GenericLab/TurbiGnUSB/TurbidiGnUSB_PCB/Turbidignusb.sch

## KiCad design TurbidiGnUSB_PCB/Turbidignusb.sch (2016-08-07)

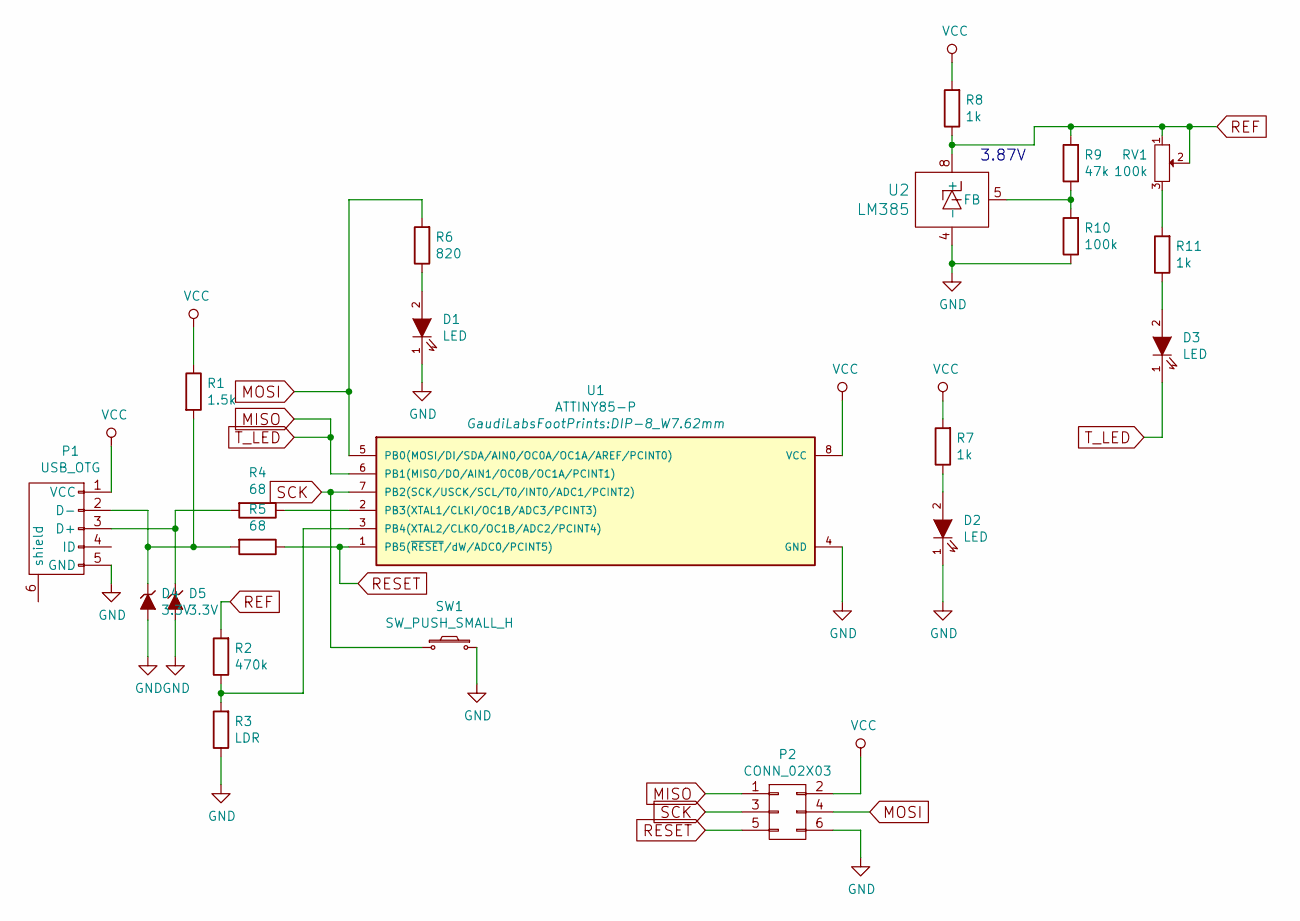
[picture p7: schematic Turbidignusb.sch]

Parts:
D1, D2: LED; Fuse_SMD1206_HandSoldering
D3: LED; SolderWirePad_2x0_8_oval
D4, D5: 3.3V; C_1206_HandSoldering
P1: USB_OTG; USB_Micro-B
P2: CONN_02X03; Pin_Header_Straight_2x03
R1: 1.5k; 0805G
R2: 470k; 0805G
R3: LDR; SolderWirePad_2x0_8_oval
R4, R5: 68; 0805G
R6: 820; 0805G
R7, R8, R11: 1k; 0805G
R9: 47k; 0805G
R10: 100k; 0805G
RV1: 100k; Potentiometer_Bourns_3296Y_3-8Zoll_Angular_ScrewUp
SW1: SW_PUSH_SMALL_H; PUSH_BUTTON_SMD
U1: ATTINY85-P; DIP-8_W7.62mm
U2: LM385; SO08

Connections:
GND: D1.1 (K), D2.1 (K), D4.2 (A), D5.2 (A), P1.5 (GND), P2.6, R3.1, R10.1, SW1.2, U1.4 (GND), U2.4 (-)
MISO: D3.1 (K), P2.1, U1.6 (PB1(MISO/DO/AIN1/OC0B/OC1A/PCINT1))
MOSI: P2.4, R6.2, U1.5 (PB0(MOSI/DI/SDA/AIN0/OC0A/OC1A/AREF/PCI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)
unnamed: D1.2 (A), R6.1
unnamed: D2.2 (A), R7.1
unnamed: D3.2 (A), R11.1
unnamed: D4.1 (K), P1.2 (D-), R1.2, R5.2
unnamed: D5.1 (K), P1.3 (D+), R4.2
unnamed: R2.1, R3.2, U1.3 (PB4(XTAL2/CLKO/OC1B/ADC2/PCINT4))
unnamed: R4.1, U1.2 (PB3(XTAL1/CLKI/OC1B/ADC3/PCINT3))
unnamed: R9.1, R10.2, U2.5 (FB)
unnamed: R11.2, RV1.3
REF: R2.2, R8.1, R9.2, RV1.1, RV1.2, U2.8 (+)
RESET: P2.5, R5.1, U1.1 (PB5(~RESET~/dW/ADC0/PCINT5))
SCK: P2.3, SW1.1, U1.7 (PB2(SCK/USCK/SCL/T0/INT0/ADC1/PCINT2))
VCC: P1.1 (VCC), P2.2, R1.1, R7.2, R8.2, U1.8 (VCC)

Notes on the sheet:
3.87V
